Bleuarff/station-meteo/schematics/satellite-indoor.kicad_sch

## KiCad design schematics/satellite-indoor.kicad_sch (2024-05-29)

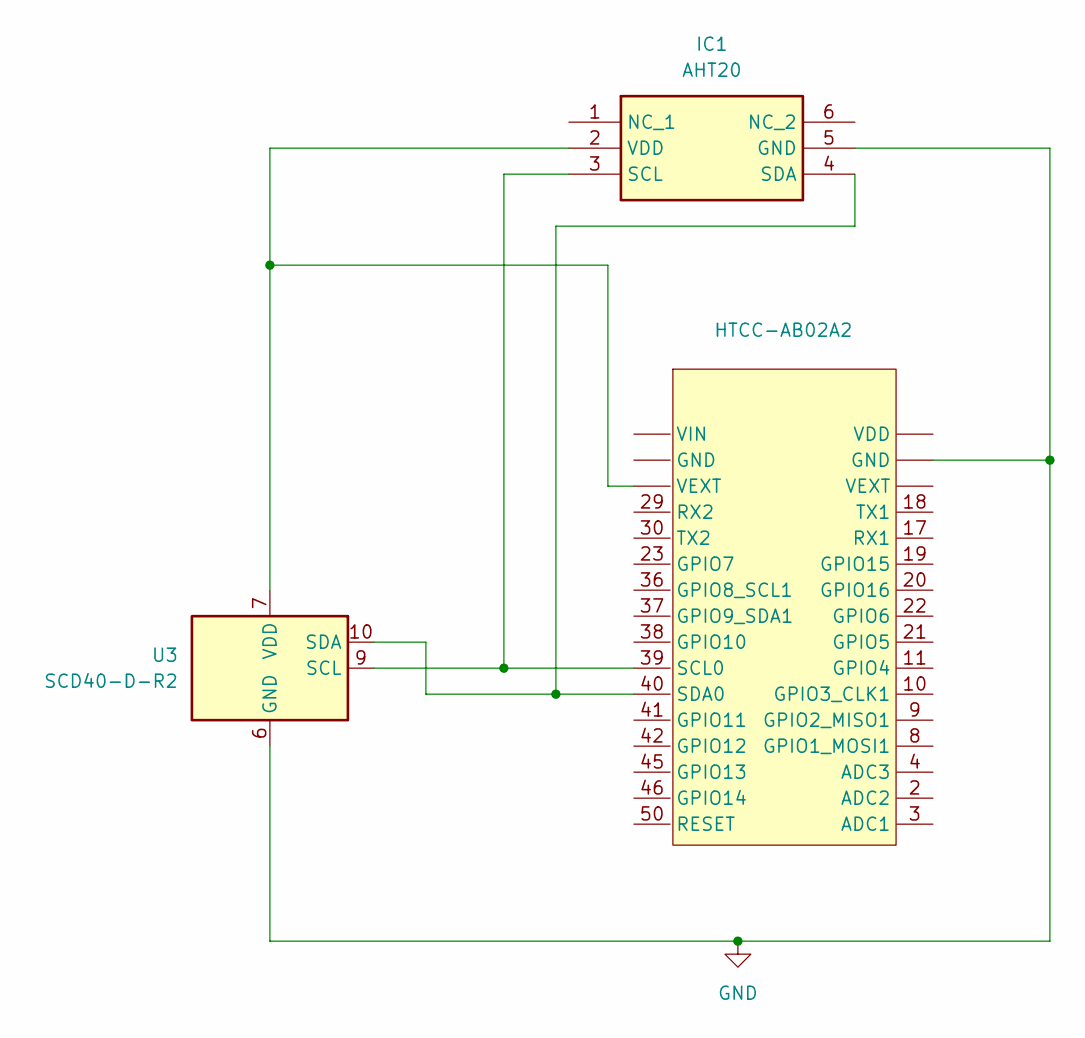
[picture p2: schematic satellite-indoor.kicad_sch]

Parts:
HTCC-AB02A2: (no value)
IC1: AHT20; Manufacturer_Part_Number AHT20
U3: SCD40-D-R2; Sensirion_SCD4x-1EP_10.1x10.1mm_P1.25mm_EP4.8x4.8mm

Connections:
GND: HTCC-AB02A2. (GND), IC1.5 (GND), U3.6 (GND), U3.20 (GND), U3.21 (GND)
unnamed: HTCC-AB02A2.39 (SCL0), IC1.3 (SCL), U3.9 (SCL)
unnamed: HTCC-AB02A2.40 (SDA0), IC1.4 (SDA), U3.10 (SDA)
unnamed: HTCC-AB02A2. (GND), IC1.2 (VDD), U3.7 (VDD), U3.19 (VDD)
