Bleuarff/station-meteo/schematics/satellite-outdoor.kicad_sch

## KiCad design schematics/satellite-outdoor.kicad_sch (2024-05-31)

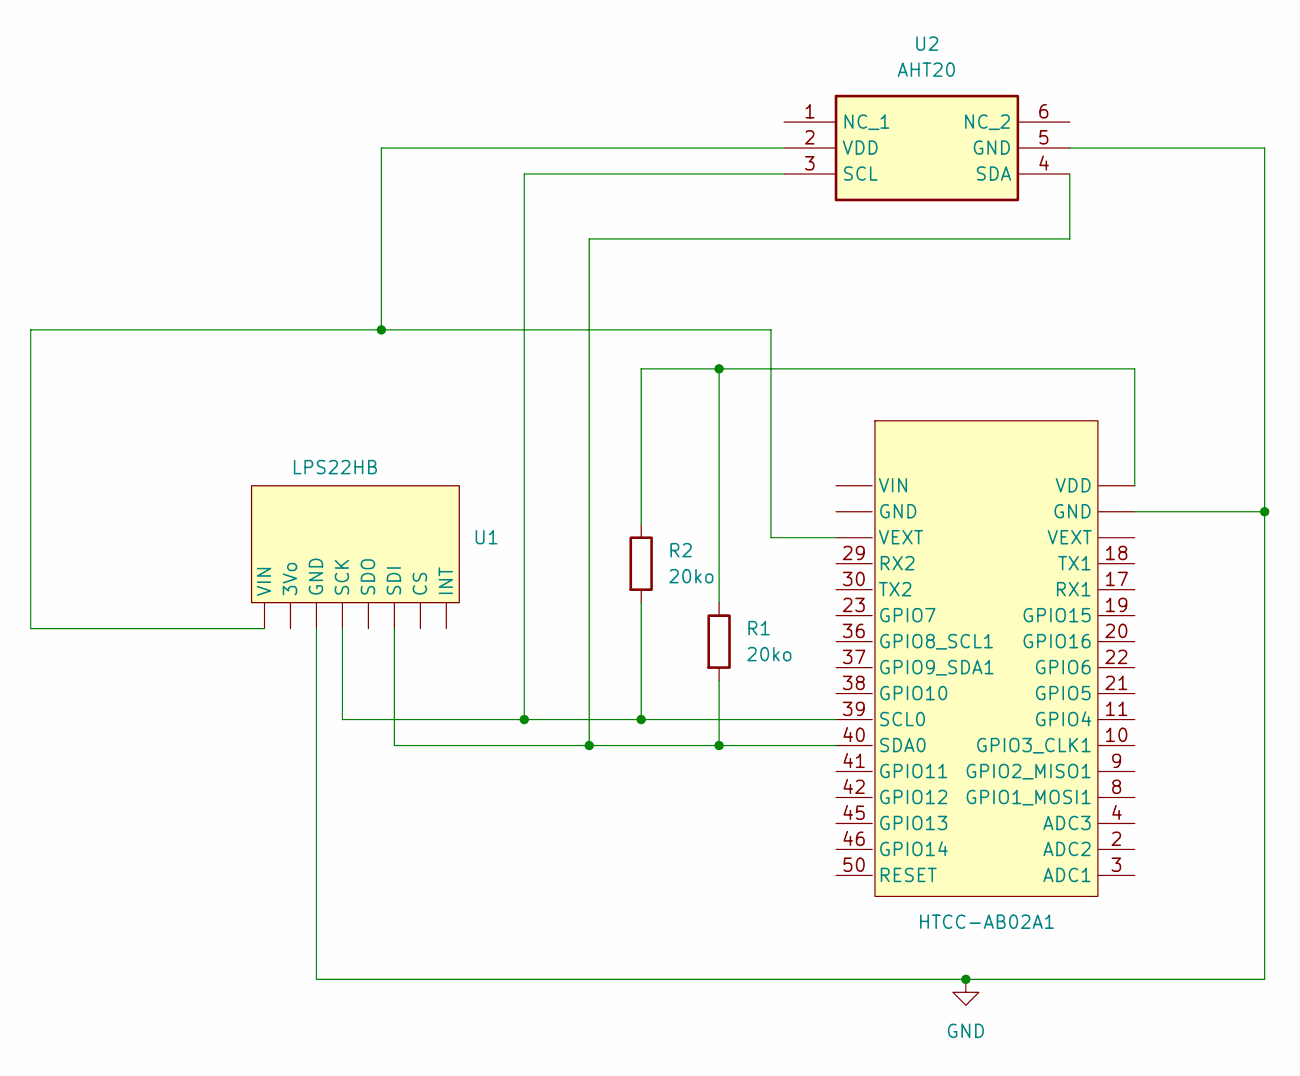
[picture p3: schematic satellite-outdoor.kicad_sch]

Parts:
HTCC-AB02A1: (no value)
R1, R2: 20ko
U1: LPS22HB
U2: AHT20; Manufacturer_Part_Number AHT20

Connections:
GND: HTCC-AB02A1. (GND), U1., U2.5 (GND)
unnamed: HTCC-AB02A1.39 (SCL0), R2.2, U1., U2.3 (SCL)
unnamed: HTCC-AB02A1.40 (SDA0), R1.2, U1., U2.4 (SDA)
unnamed: HTCC-AB02A1. (GND), R1.1, R2.1, U1., U2.2 (VDD)
