Bleuarff/station-meteo/schematics/station-meteo.kicad_sch

## KiCad design schematics/station-meteo.kicad_sch (2024-05-31)

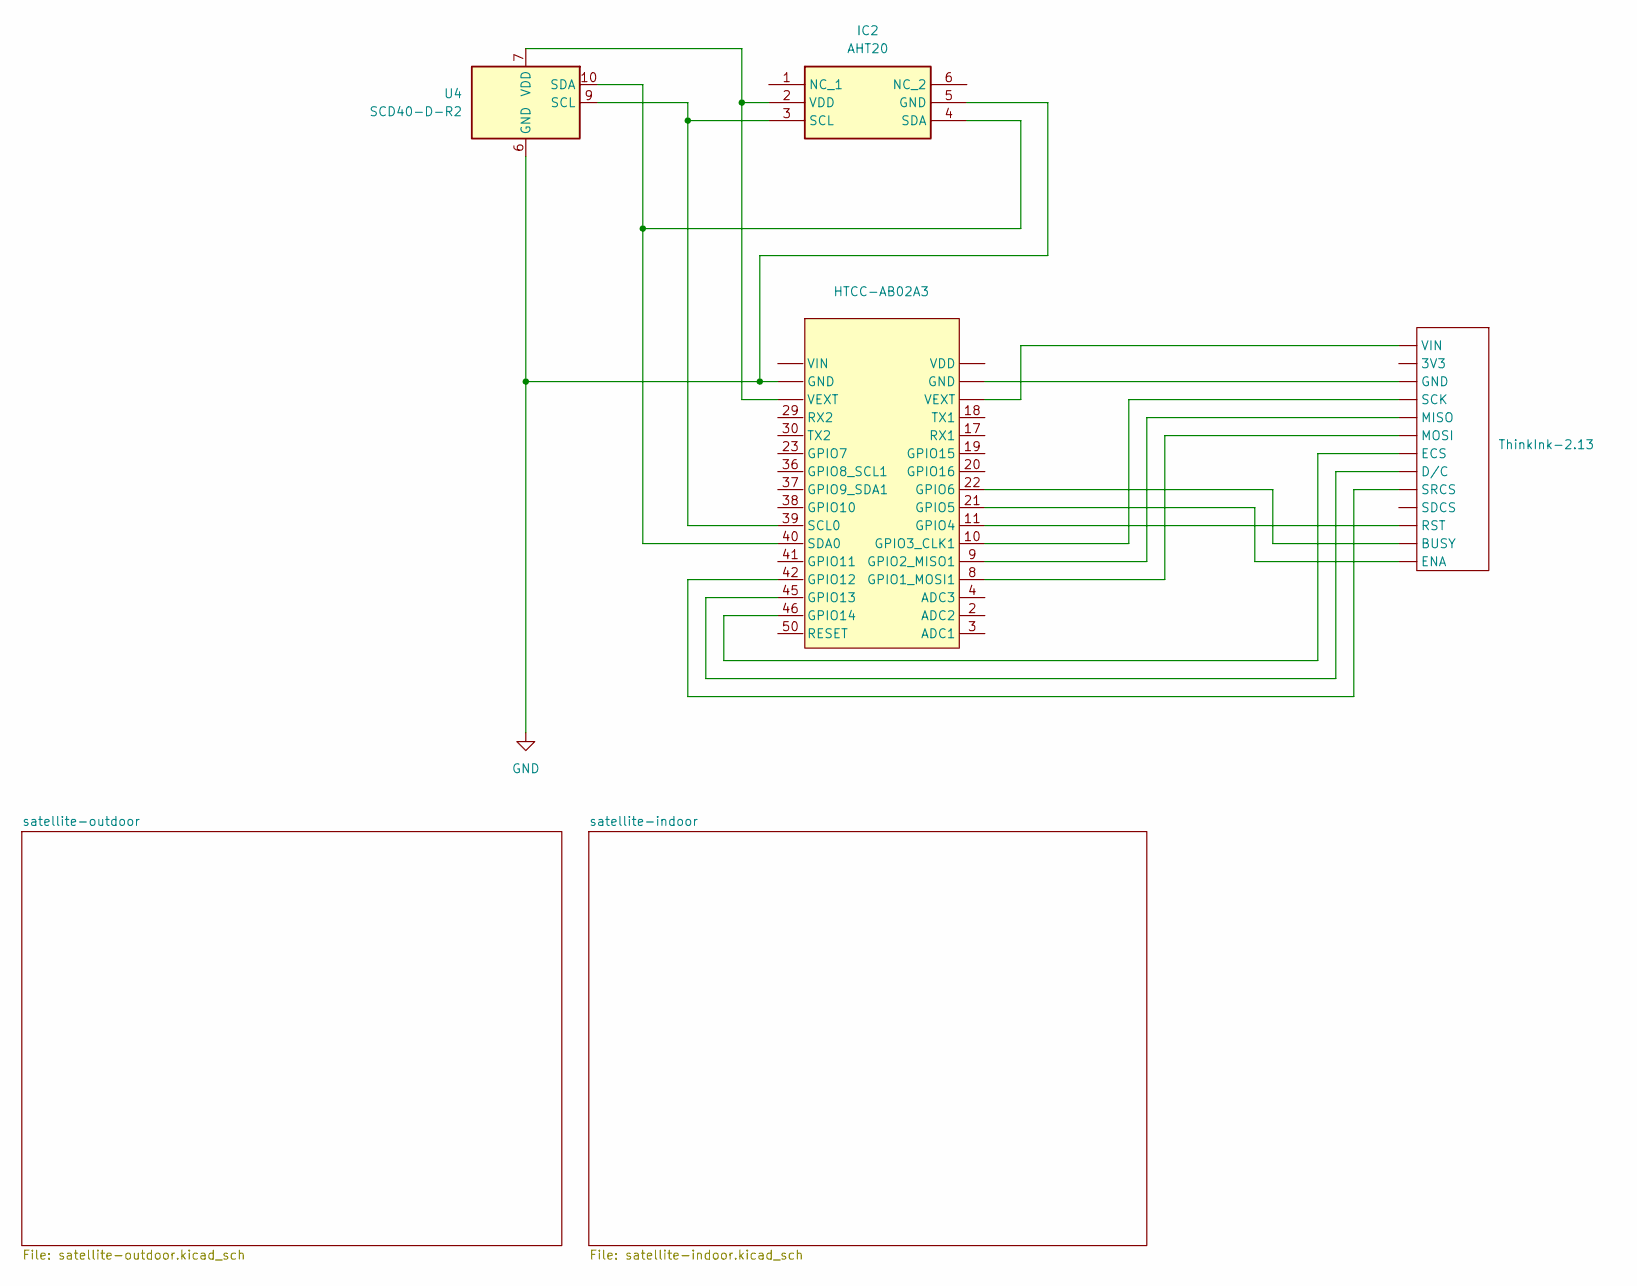
[picture p4: schematic station-meteo.kicad_sch]

Parts:
HTCC-AB02A3: (no value)
IC2: AHT20; Manufacturer_Part_Number AHT20
ThinkInk-2.13: (no value)
U4: SCD40-D-R2; Sensirion_SCD4x-1EP_10.1x10.1mm_P1.25mm_EP4.8x4.8mm

Connections:
GND: HTCC-AB02A3. (GND), IC2.5 (GND), U4.6 (GND), U4.20 (GND), U4.21 (GND)
unnamed: HTCC-AB02A3.8 (GPIO1_MOSI1), ThinkInk-2.13.
unnamed: HTCC-AB02A3.9 (GPIO2_MISO1), ThinkInk-2.13.
unnamed: HTCC-AB02A3.10 (GPIO3_CLK1), ThinkInk-2.13.
unnamed: HTCC-AB02A3.11 (GPIO4), ThinkInk-2.13.
unnamed: HTCC-AB02A3.21 (GPIO5), ThinkInk-2.13.
unnamed: HTCC-AB02A3.22 (GPIO6), ThinkInk-2.13.
unnamed: HTCC-AB02A3.39 (SCL0), IC2.3 (SCL), U4.9 (SCL)
unnamed: HTCC-AB02A3.40 (SDA0), IC2.4 (SDA), U4.10 (SDA)
unnamed: HTCC-AB02A3.42 (GPIO12), ThinkInk-2.13.
unnamed: HTCC-AB02A3.45 (GPIO13), ThinkInk-2.13.
unnamed: HTCC-AB02A3.46 (GPIO14), ThinkInk-2.13.
unnamed: HTCC-AB02A3. (GND), IC2.2 (VDD), ThinkInk-2.13., U4.7 (VDD), U4.19 (VDD)
